willsowerbutts/tv-controller/scope-pics/capture-mute.png

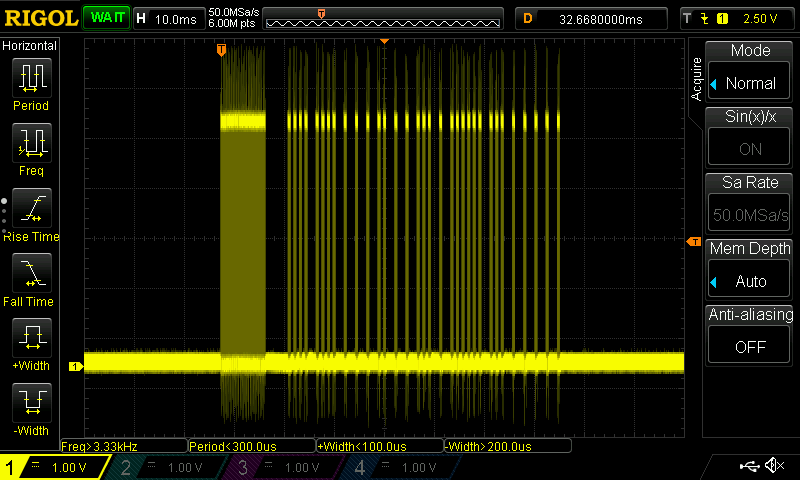
scope-pics/capture-mute.png
