willsowerbutts/tv-controller/kicad/IRBoard/IRBoard.kicad_sch

## KiCad design kicad/IRBoard/IRBoard.kicad_sch (2025-01-25)

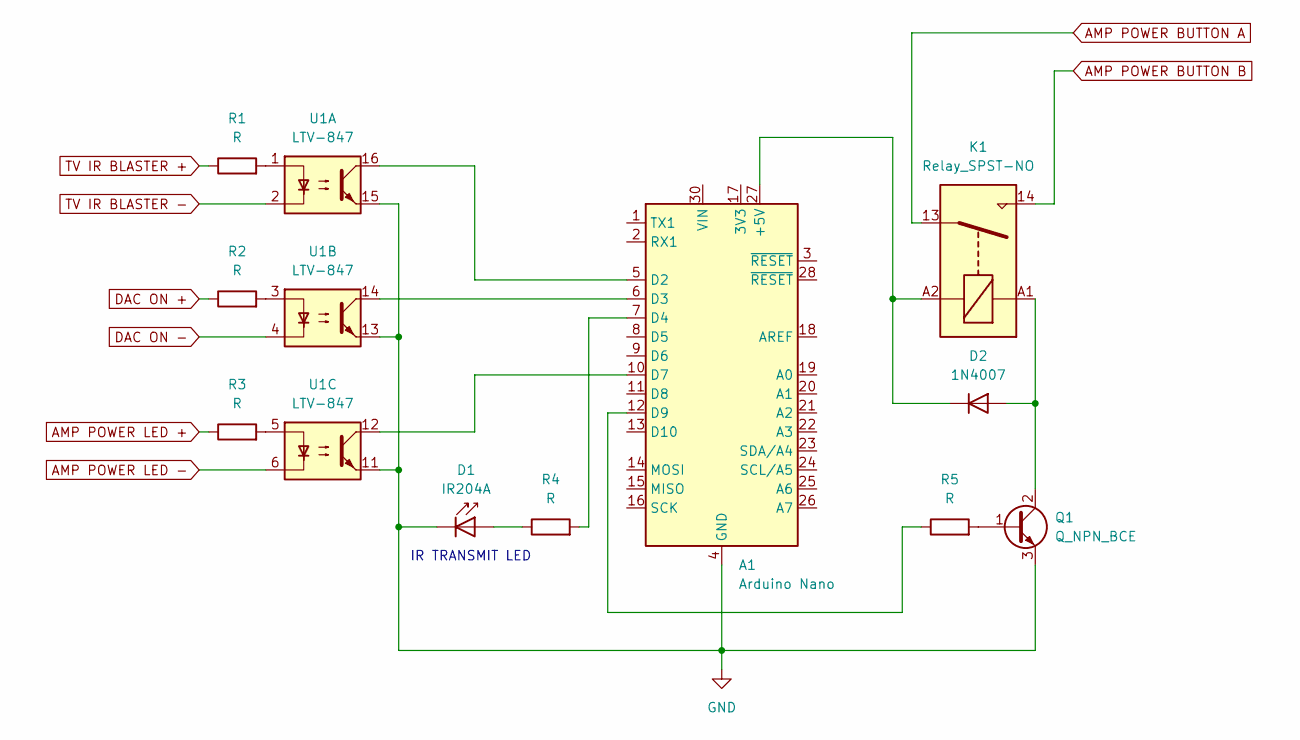
[picture p5: schematic IRBoard.kicad_sch]

Parts:
A1: Arduino Nano; Arduino_Nano
D1: IR204A; LED_D3.0mm_IRBlack
D2: 1N4007; D_DO-41_SOD81_P10.16mm_Horizontal
K1: Relay_SPST-NO
Q1: Q_NPN_BCE
R1, R2, R3, R4, R5: R
U1: LTV-847; DIP-16_W7.62mm

Connections:
AMP POWER BUTTON A: K1.13
AMP POWER BUTTON B: K1.14
AMP POWER LED +: R3.1
AMP POWER LED -: U1.6
DAC ON +: R2.1
DAC ON -: U1.4
GND: A1.4 (GND), A1.29 (GND), D1.1 (K), Q1.3 (E), U1.11, U1.13, U1.15
unnamed: A1.5 (D2), U1.16
unnamed: A1.6 (D3), U1.14
unnamed: A1.7 (D4), R4.2
unnamed: A1.10 (D7), U1.12
unnamed: A1.12 (D9), R5.1
unnamed: A1.27 (+5V), D2.1 (K), K1.A2
unnamed: D1.2 (A), R4.1
unnamed: D2.2 (A), K1.A1, Q1.2 (C)
unnamed: Q1.1 (B), R5.2
unnamed: R1.2, U1.1
unnamed: R2.2, U1.3
unnamed: R3.2, U1.5
TV IR BLASTER +: R1.1
TV IR BLASTER -: U1.2

Notes on the sheet:
IR TRANSMIT LED
